djmason9/WeatherStation/CustomDisplayFonts.h

// uint8_t
// Created by http://oleddisplay.squix.ch/ Consider a donation
// In case of problems make sure that you are using the font file with the correct version!
const uint8_t SansSerif_plain_12[] PROGMEM = {
	0x0D, // Width: 13
	0x0F, // Height: 15
	0x20, // First Char: 32
	0xE0, // Numbers of Chars: 224

	// Jump Table:
	0xFF, 0xFF, 0x00, 0x04,  // 32:65535
	0x00, 0x00, 0x06, 0x05,  // 33:0
	0x00, 0x06, 0x07, 0x05,  // 34:6
	0x00, 0x0D, 0x11, 0x0A,  // 35:13
	0x00, 0x1E, 0x0E, 0x08,  // 36:30
	0x00, 0x2C, 0x14, 0x0B,  // 37:44
	0x00, 0x40, 0x12, 0x0A,  // 38:64
	0x00, 0x52, 0x03, 0x03,  // 39:82
	0x00, 0x55, 0x08, 0x05,  // 40:85
	0x00, 0x5D, 0x08, 0x05,  // 41:93
	0x00, 0x65, 0x0B, 0x06,  // 42:101
	0x00, 0x70, 0x10, 0x0A,  // 43:112
	0x00, 0x80, 0x04, 0x04,  // 44:128
	0x00, 0x84, 0x08, 0x04,  // 45:132
	0x00, 0x8C, 0x04, 0x04,  // 46:140
	0x00, 0x90, 0x07, 0x04,  // 47:144
	0x00, 0x97, 0x0E, 0x08,  // 48:151
	0x00, 0xA5, 0x0C, 0x08,  // 49:165
	0x00, 0xB1, 0x0E, 0x08,  // 50:177
	0x00, 0xBF, 0x0E, 0x08,  // 51:191
	0x00, 0xCD, 0x0E, 0x08,  // 52:205
	0x00, 0xDB, 0x0E, 0x08,  // 53:219
	0x00, 0xE9, 0x0E, 0x08,  // 54:233
	0x00, 0xF7, 0x0D, 0x08,  // 55:247
	0x01, 0x04, 0x0E, 0x08,  // 56:260
	0x01, 0x12, 0x0E, 0x08,  // 57:274
	0x01, 0x20, 0x04, 0x04,  // 58:288
	0x01, 0x24, 0x04, 0x04,  // 59:292
	0x01, 0x28, 0x12, 0x0A,  // 60:296
	0x01, 0x3A, 0x12, 0x0A,  // 61:314
	0x01, 0x4C, 0x12, 0x0A,  // 62:332
	0x01, 0x5E, 0x09, 0x06,  // 63:350
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
	0x00,0x00,0xF8,0x03,0x48,0x02,0x48,0x02,0x48,0x02,0x48,0x02,	// 69
	0x00,0x00,0xF8,0x03,0x48,0x00,0x48,0x00,0x48,	// 70
	0x00,0x00,0xF0,0x01,0x18,0x03,0x08,0x02,0x48,0x02,0x48,0x02,0xD0,0x01,	// 71
	0x00,0x00,0xF8,0x03,0x40,0x00,0x40,0x00,0x40,0x00,0x40,0x00,0xF8,0x03,	// 72
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
};
