djmason9/WeatherStation/MoonPhase.h

const unsigned char newMoon [] =  {
0x00, 0x00, 0x00, 0x00, 0x00, 0x00, 0x00, 0x00, 0x00, 0x00, 0x00, 0x00, 
0x00, 0x00, 0x00, 0x00, 0x80, 0x03, 0x00, 0x00, 0x00, 0x00, 0x00, 0xFC, 
0x7F, 0x00, 0x00, 0x00, 0x00, 0x80, 0xFF, 0xFF, 0x03, 0x00, 0x00, 0x00, 
0xE0, 0x07, 0xC0, 0x0F, 0x00, 0x00, 0x00, 0xF0, 0x00, 0x00, 0x1E, 0x00, 
0x00, 0x00, 0x3C, 0x00, 0x00, 0x78, 0x00, 0x00, 0x00, 0x1E, 0x00, 0x00, 
0xF0, 0x00, 0x00, 0x00, 0xCF, 0x07, 0x00, 0xC0, 0x01, 0x00, 0x80, 0xE7, 
0x0F, 0x00, 0x80, 0x03, 0x00, 0x80, 0xF3, 0x1F, 0x00, 0x00, 0x07, 0x00, 
0xC0, 0xF1, 0x1F, 0x1C, 0x00, 0x07, 0x00, 0xE0, 0xF0, 0x1F, 0x7E, 0x00, 
0x0E, 0x00, 0x60, 0xF0, 0x1F, 0x7E, 0x00, 0x0C, 0x00, 0x70, 0xF0, 0x1F, 
0x7E, 0x00, 0x1C, 0x00, 0x30, 0xE0, 0x0F, 0x7E, 0x80, 0x18, 0x00, 0x38, 
0xC0, 0x07, 0xFE, 0xC1, 0x39, 0x00, 0x38, 0x00, 0x00, 0xF8, 0xC3, 0x31, 
0x00, 0x18, 0x00, 0x00, 0xF0, 0xC3, 0x31, 0x00, 0x18, 0x00, 0x00, 0xF0, 
0x03, 0x70, 0x00, 0x1C, 0x00, 0x00, 0xF0, 0x03, 0x70, 0x00, 0x1C, 0x00, 
0x00, 0xE0, 0x73, 0x60, 0x00, 0x1C, 0x00, 0x00, 0x80, 0xF8, 0x60, 0x00, 
0x1C, 0x00, 0x00, 0x00, 0xFC, 0x61, 0x00, 0x1C, 0x00, 0x00, 0x00, 0xFC, 
0x61, 0x00, 0x1C, 0x00, 0x00, 0x00, 0xFC, 0x61, 0x00, 0x1C, 0x00, 0x00, 
0x00, 0xFC, 0x71, 0x00, 0x1C, 0x00, 0x04, 0x00, 0xF8, 0x70, 0x00, 0x18, 
0x00, 0x0E, 0x00, 0x70, 0x70, 0x00, 0x18, 0x00, 0x0E, 0x00, 0x00, 0x30, 
0x00, 0x38, 0x00, 0x00, 0x00, 0x00, 0x30, 0x00, 0x30, 0x00, 0x07, 0x00, 
0x00, 0x38, 0x00, 0x30, 0x80, 0x0F, 0x00, 0x00, 0x18, 0x00, 0x70, 0x80, 
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
0x00, 0x00, 0xF0, 0x3F, 0x80, 0x0F, 0x00, 0x00, 0x00, 0xE0, 0x7F, 0xF0, 
0x03, 0x00, 0x00, 0x00, 0x80, 0xFF, 0xFF, 0x00, 0x00, 0x00, 0x00, 0x00, 
0xFC, 0x1F, 0x00, 0x00, 0x00, 0x00, 0x00, 0x00, 0x00, 0x00, 0x00, 0x00, 
0x00, 0x00, 0x00, 0x00, 0x00, 0x00, 0x00, 
 };
